dchwebb/Quango/Quango/src/tuner.cpp

#include "tuner.h"
#include "VoiceManager.h"
#include <cstring>

Tuner tuner;

void Tuner::Capture()
{
	GPIOD->ODR |= GPIO_ODR_OD0;			// Toggle test pin 1

	bool samplesReady = false;
	if (mode == FFT) {

		float* floatBuffer = (float*)&(fft.fftBuffer);
		floatBuffer[bufferPos] = 2047.0f - static_cast<float>(adc.PitchDetect);

		// Capture 1.5 buffers - if capturing last third add it to the 2nd half of buffer 2
		// 1st half of buffer 2 will be populated later from 2nd half of buffer 1
		if (++bufferPos == FFT::fftSamples) {
			bufferPos += FFT::fftSamples / 2;
		}
		if (bufferPos > FFT::fftSamples * 2) {
			samplesReady = true;
		}
	} else {
		++timer;

		if (overZero && static_cast<int>(adc.PitchDetect) < calibZeroPos - 100) {
			overZero = false;
		}
		if (!overZero && adc.PitchDetect > calibZeroPos) {
			overZero = true;
			zeroCrossings[bufferPos] = timer;
			if (++bufferPos == zeroCrossings.size()) {
				samplesReady = true;
			}
		}

		// If no signal found abort and display no signal message
		if (timer > 200000) {
			samplesReady = true;
		}
	}

	GPIOD->ODR &= ~GPIO_ODR_OD0;			// Toggle test pin 1

	if (samplesReady) {
		TIM5->CR1 &= ~TIM_CR1_CEN;					// Disable the sample acquisiton timer
		CalcFreq();
	}
}


bool Tuner::CheckStart()
{
	// check if calibration button is pressed (PB10 - channel A, PB11 - channel B)
	if ((GPIOB->IDR & GPIO_IDR_ID10) == 0 && !running) {				// PB10: channel A
		running = true;
		voiceManager.calibrating = true;

		// set Envelopes to silent
		for (auto c : voiceManager.channel) {
			for (auto v : c.voice) {
				v.envelope.SetEnvelope(0);
			}
		}

		// set pitch to A2 (midi note 57)
		voiceManager.channel[VoiceManager::channelA].voice[0].midiNote = 69;
		voiceManager.channel[VoiceManager::channelA].voice[0].SetPitch(VoiceManager::channelA);
		currFreq = 220.0f;
		voiceManager.channel[VoiceManager::channelA].voice[0].envelope.SetEnvelope(4095);

		// start tuner
		Activate(true);
	}
	return running;
}


void Tuner::Activate(bool startTimer)
{
	if (mode == FFT) {
		if (currFreq > 800.0f) {
			TIM5->ARR = (FFT::timerDefault / 2) + sampleRateAdj;
		} else if (currFreq < 50.0f) {
			TIM5->ARR = (FFT::timerDefault * 2) + sampleRateAdj;
		} else {
			TIM5->ARR = FFT::timerDefault + sampleRateAdj;
		}
	} else {
		// Get current value of ADC (assume channel A for now)
		const uint32_t currVal = adc.PitchDetect;
		overZero = currVal > calibZeroPos;
		timer = 0;
		TIM5->ARR = zeroCrossRate;
	}

	bufferPos = 0;

	if (startTimer) {
		TIM5->CR1 |= TIM_CR1_CEN;
	}
}



void Tuner::CalcFreq()
{
	float frequency = 0.0f;
	const uint32_t start = SysTickVal;

	if (mode == FFT) {
		// Phase adjusted FFT: FFT on two overlapping buffers; where the 2nd half of buffer 1 is the 1st part of buffer 2
		// Calculate the fundamental bin looking for a magnitude over a threshold, then adjust by the phase difference of the two FFTs

		// As we do two FFTs on samples 0 - 1023 then 512 - 1535, copy samples 512 - 1023 to position 1024
		memcpy(&(fft.fftBuffer[1]), &(fft.fftBuffer[0][512]), 512 * 4);

		fft.CalcFFT(fft.fftBuffer[0], FFT::fftSamples);			// Carry out FFT on first buffer

		// Find first significant harmonic
		volatile uint32_t fundMag = 0;
		volatile uint32_t maxMag = 0;
		volatile uint32_t maxBin = 0;
		bool localMax = false;			// True once magnitude of bin is large enough to count as fundamental

		// Locate maximum hypoteneuse
		for (uint32_t i = 1; i < FFT::fftSamples / 2; ++i) {
			const float hypotenuse = std::hypot(fft.fftBuffer[0][i], fft.cosBuffer[i]);
			if (hypotenuse > maxMag) {
				maxMag = hypotenuse;
			}
		}

		// Locate first hypoteuse that is large enough relative to the maximum to count as fundamental
		for (uint32_t i = 1; i < FFT::fftSamples / 2; ++i) {
			const float hypotenuse = std::hypot(fft.fftBuffer[0][i], fft.cosBuffer[i]);
			if (localMax) {
				if (hypotenuse > fundMag) {
					fundMag = hypotenuse;
					maxBin = i;
				} else {
					break;
				}
			} else if (hypotenuse > magThreshold && hypotenuse > static_cast<float>(maxMag) * 0.5f) {
				localMax = true;
				fundMag = hypotenuse;
				maxBin = i;
			}
		}

		if (maxBin) {

			volatile const float phase0 = atan(fft.cosBuffer[maxBin] / fft.fftBuffer[0][maxBin]);

			fft.CalcFFT(fft.fftBuffer[1], FFT::fftSamples);				// Carry out FFT on buffer 2 (overwrites cosine results from first FFT)

			volatile const float phase1 = atan(fft.cosBuffer[maxBin] / fft.fftBuffer[1][maxBin]);
			volatile float phaseAdj = (phase0 - phase1) / M_PI;			// normalise phase adjustment

			// handle phase wrapping
			if (phaseAdj < -0.5f) {
				phaseAdj += 1.0f;
			}
			if (phaseAdj > 0.5f) {
				phaseAdj -= 1.0f;
			}

			// When a signal is almost exactly between two bins the first and second FFT can disagree
			// Use the direction of the phase adjustment to correct
			volatile const uint32_t hyp11 = std::hypot(fft.fftBuffer[1][maxBin + 0], fft.cosBuffer[maxBin + 0]);
			volatile const uint32_t hyp12 = std::hypot(fft.fftBuffer[1][maxBin + 1], fft.cosBuffer[maxBin + 1]);
			if (hyp12 > hyp11 && phaseAdj < 0.0f) {		// Correct for situations where each FFT disagrees about the fundamental bin
				++maxBin;
			}

			frequency = fft.HarmonicFreq(static_cast<float>(maxBin) + phaseAdj);

			// Possibly due to rounding errors at around 50% phase adjustments the cycle rate can be out by a cycle - abort and shift sampling rate
			if (phaseAdj > 0.47f || phaseAdj < -0.47f) {
				if (std::fabs(frequency - currFreq) / currFreq > 0.05f) {
					sampleRateAdj += currFreq < 60 ? 32 : 2;
					frequency = 0.0f;
				}
			}

		}

	} else {
		// Zero crossing mode
		if (bufferPos == zeroCrossings.size()) {						// Check that a signal was found

			float diff = zeroCrossings[1] - zeroCrossings[0];		// Get first time difference between zero crossings
			uint32_t stride = 1;									// Allow pitch detection where multiple zero crossings in cycle
			uint32_t noMatch = 0;									// When enough failed matches increase stride
			uint32_t matchCount = 0;

			uint32_t i;
			for (i = 1; i < zeroCrossings.size() - stride; ++i) {
				float tempDiff = zeroCrossings[i + stride] - zeroCrossings[i];

				if (tempDiff - diff < 0.05f * diff) {
					diff = (diff + tempDiff) / 2.0f;				// Apply some damping to average out differences
					++matchCount;
				} else {
					++noMatch;
					if (noMatch > 3 && stride < 10) {				// After three failures increase stride length and restart loop
						++stride;
						diff = zeroCrossings[stride] - zeroCrossings[0];
						i = 0;
						matchCount = 0;
						noMatch = 0;
					}
				}
			}

			if (matchCount > 10) {
				frequency = FreqFromPos(diff);
			}
		}
	}

	if (frequency > 16.35f) {
		currFreq = frequency;

		// Formula to get musical note from frequency is (ln(freq) - ln(16.35)) / ln(2 ^ (1/12))
		// Where 16.35 is frequency of low C and return value is semi-tones from low C
		const std::string noteNames[12] = {"C", "C#", "D", "D#", "E", "F", "F#", "G", "G#", "A", "A#", "B"};
		constexpr float numRecip = 1.0f / log(pow(2.0f, 1.0f / 12.0f));		// Store reciprocal to avoid division
		constexpr float logBase = log(16.35160f);
		float note = (log(currFreq) - logBase) * numRecip;


		const uint32_t pitch = std::lround(note) % 12;
		const uint32_t octave = std::lround(note) / 12;
		const int32_t centDiff = static_cast<int32_t>(100.0f * (note - std::round(note)));


		convBlink = !convBlink;

		lastValid = SysTickVal;

	} else if (SysTickVal - lastValid > 4000) {
		/*lcd.DrawString(30, 50, "  No Signal    ", &lcd.Font_XLarge, LCD_GREY, LCD_BLACK);
		lcd.DrawString(80, 100, ui.FloatToString(currFreq, false) + "Hz    ", &lcd.Font_XLarge, LCD_GREY, LCD_BLACK);
		*/
	}


	Activate(true);

}


float Tuner::FreqFromPos(const uint16_t pos)
{
	// returns frequency of signal based on number of samples wide the signal is versus the sampling rate
	return static_cast<float>(SystemCoreClock) / (pos * (TIM5->PSC + 1) * (TIM5->ARR + 1));
}
